mikinty/Omega3/images/IMG_20180331_031521.jpg

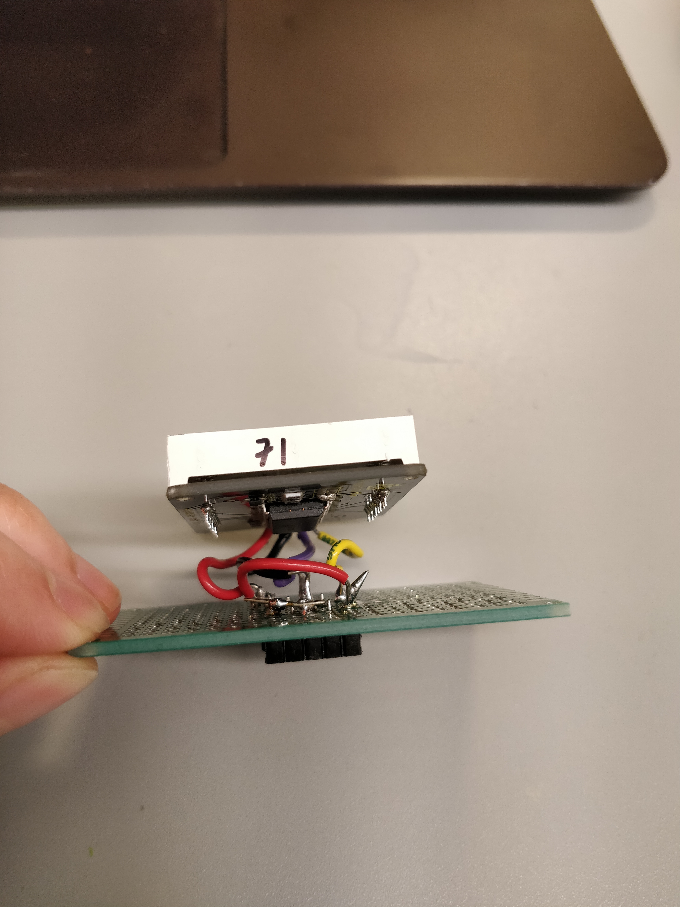
images/IMG_20180331_031521.jpg
