mikinty/Omega3/images/IMG_20180331_031531.jpg

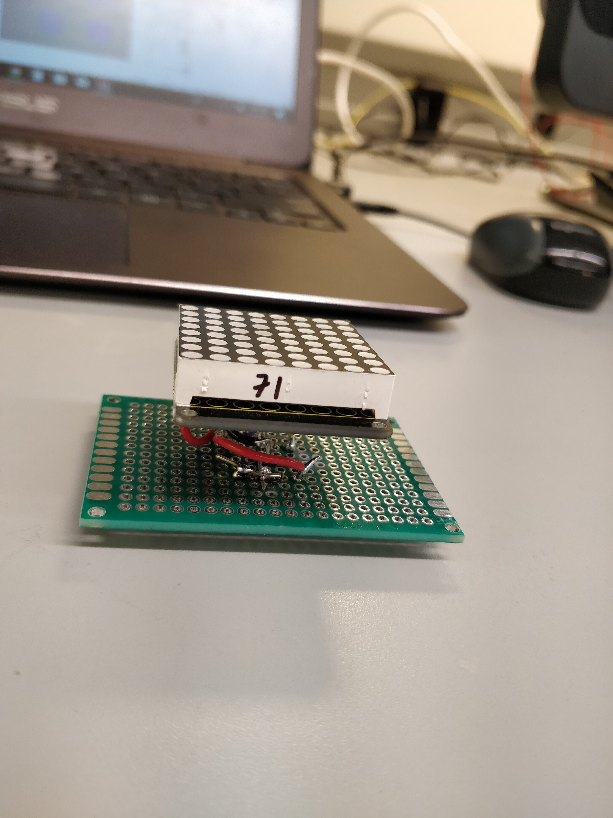
images/IMG_20180331_031531.jpg
