mikinty/Omega3/images/IMG_20180331_031629.jpg

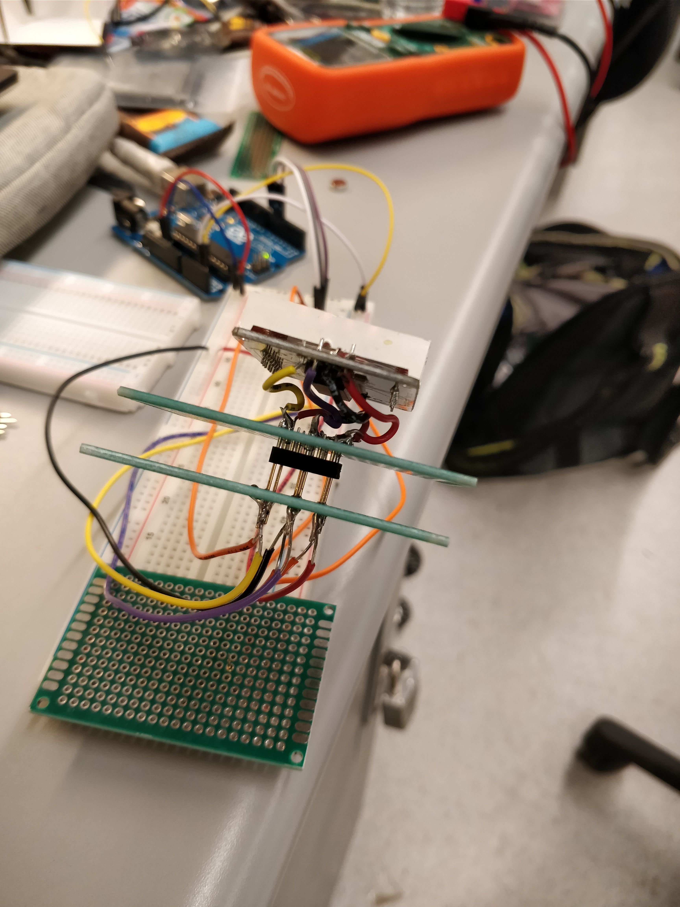
images/IMG_20180331_031629.jpg
