mikinty/Omega3/images/IMG_20180331_221203.jpg

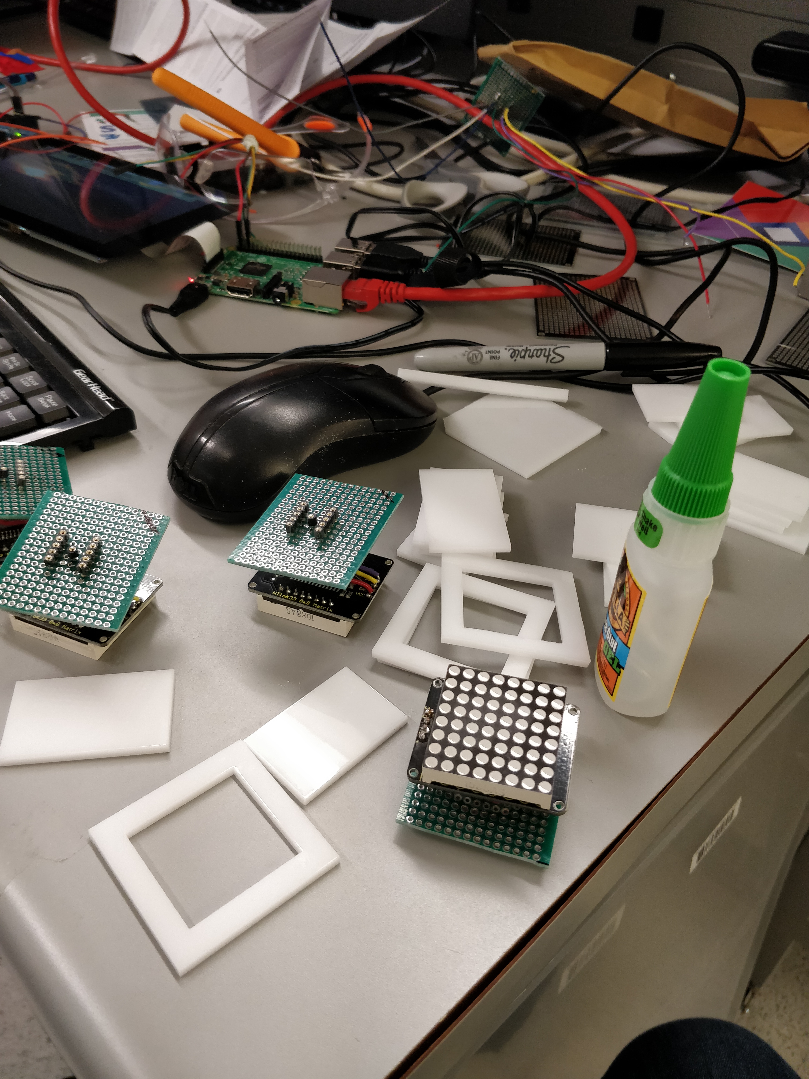
images/IMG_20180331_221203.jpg
