mikinty/Omega3/images/IMG_20180331_233230.jpg

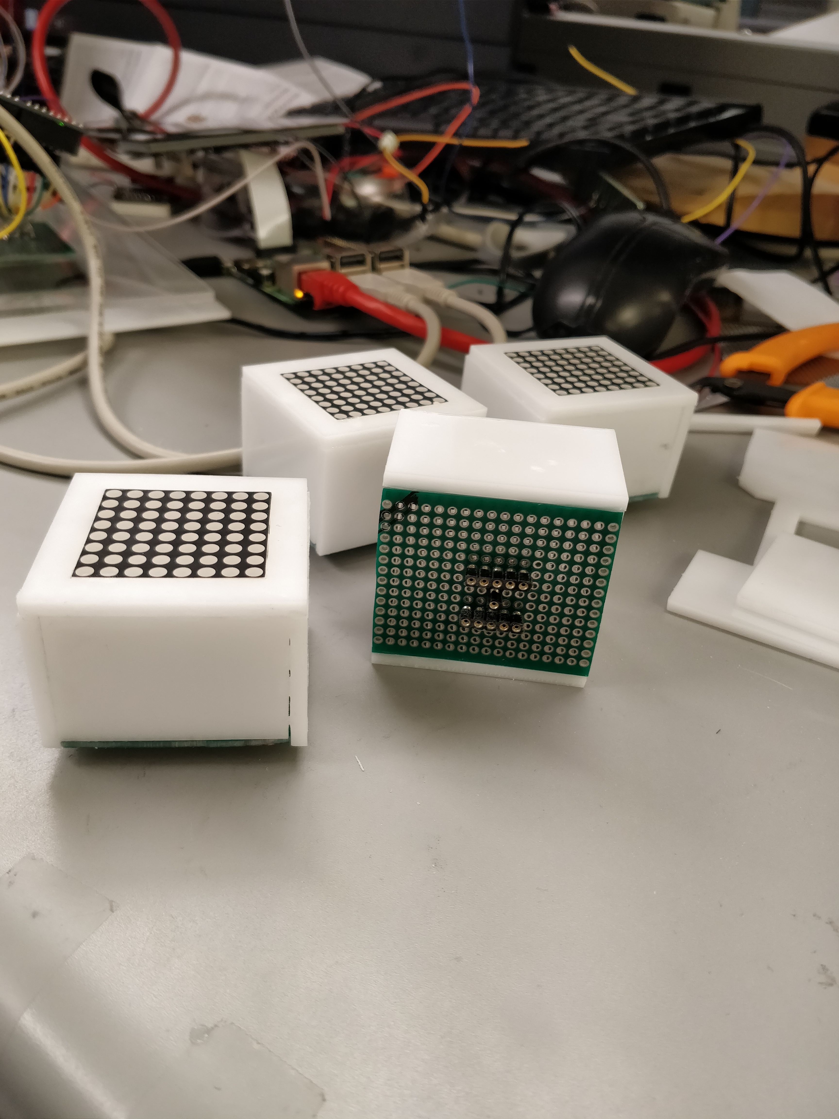
images/IMG_20180331_233230.jpg
