mikinty/Omega3/images/IMG_20180331_233232.jpg

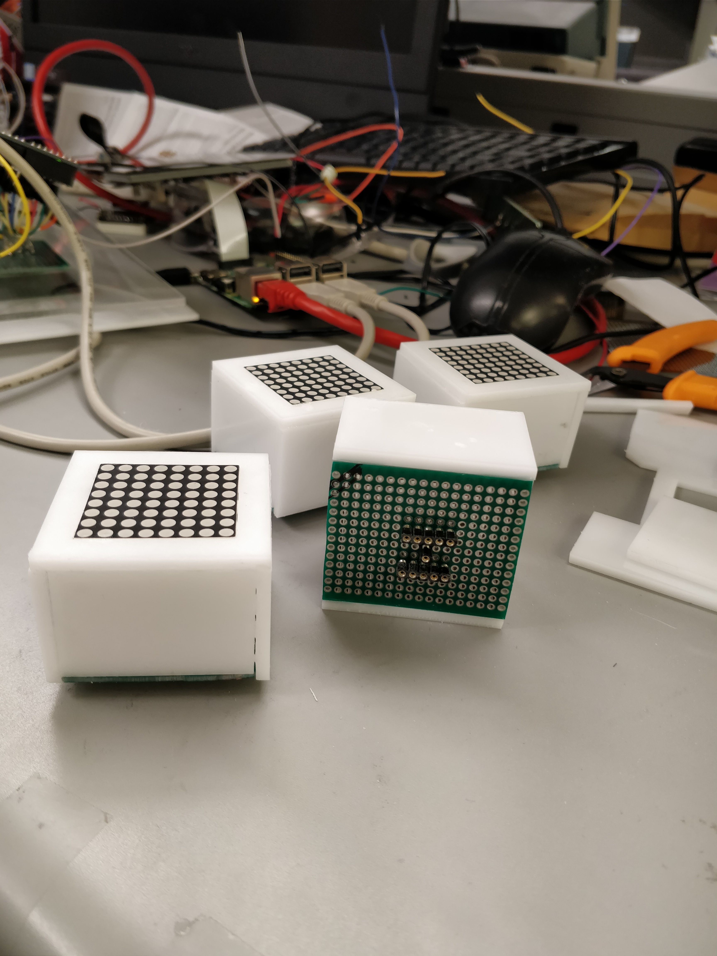
images/IMG_20180331_233232.jpg
