mikinty/Omega3/images/IMG_20180401_004014.jpg

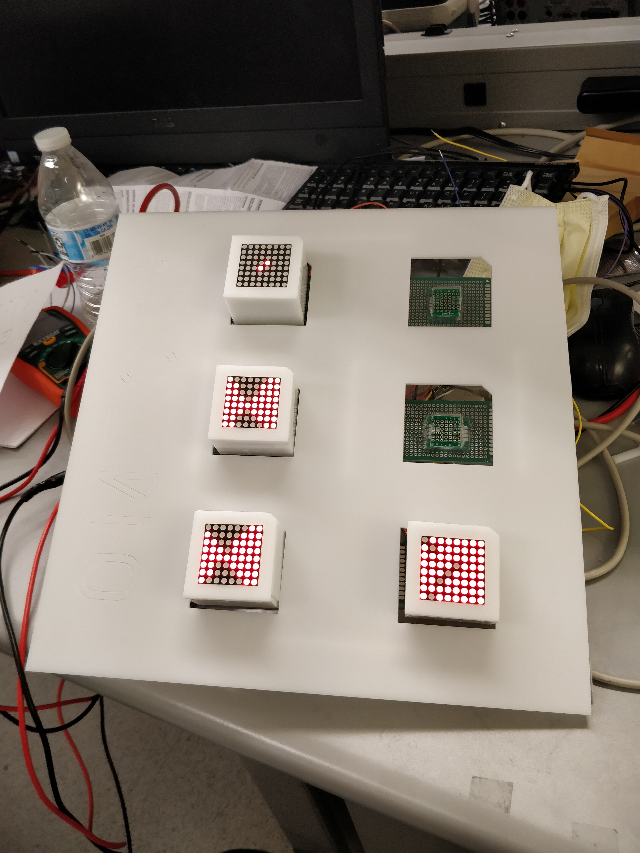
images/IMG_20180401_004014.jpg
