mikinty/Omega3/images/IMG_20180401_004016.jpg

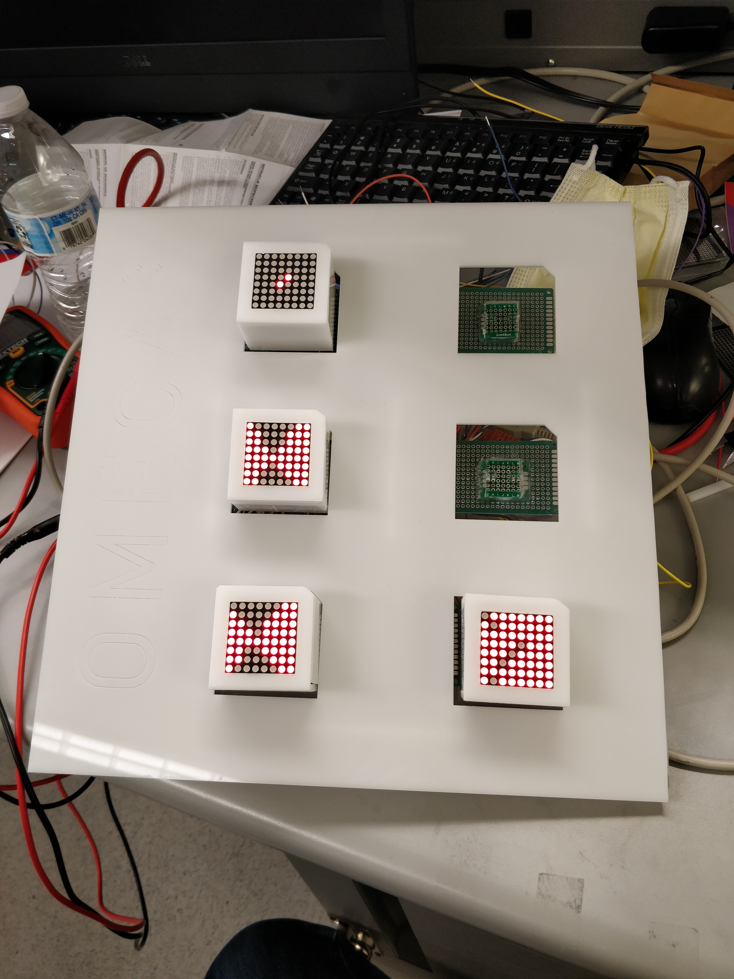
images/IMG_20180401_004016.jpg
