mikinty/Omega3/images/IMG_20180401_004311.jpg

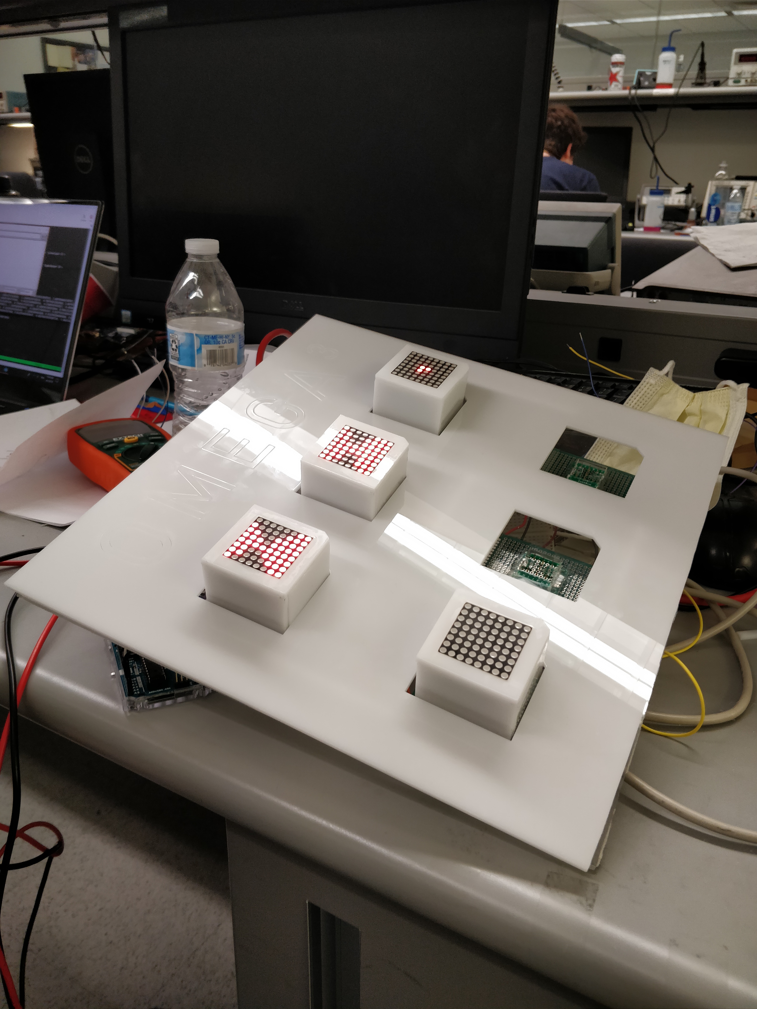
images/IMG_20180401_004311.jpg
