mikinty/Omega3/images/IMG_20180401_020950.jpg

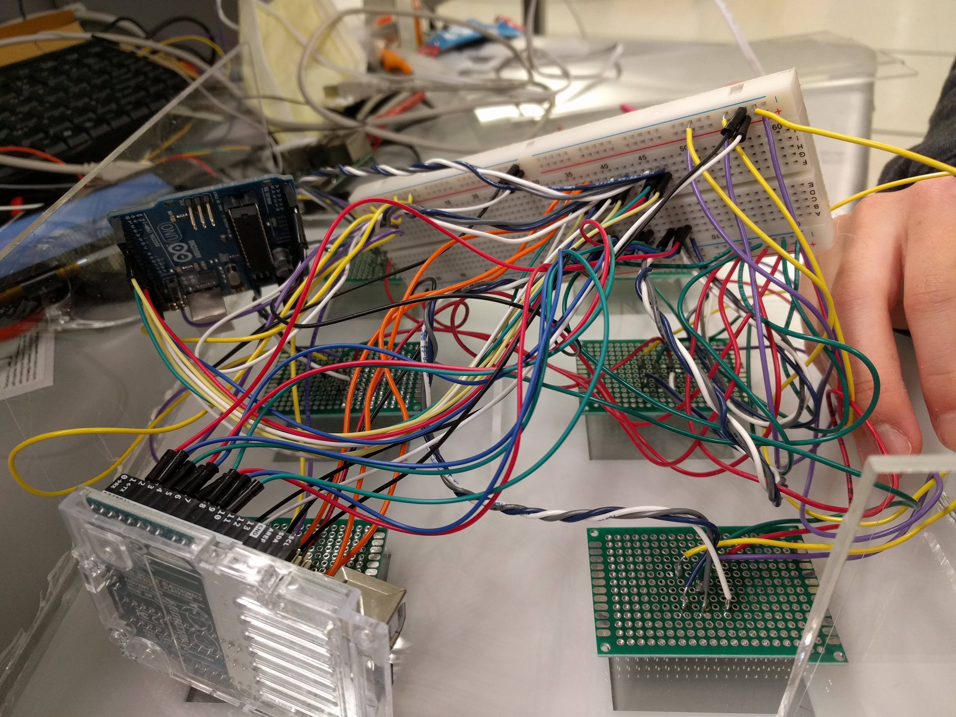
images/IMG_20180401_020950.jpg
