mikinty/Omega3/images/IMG_20180401_051516.jpg

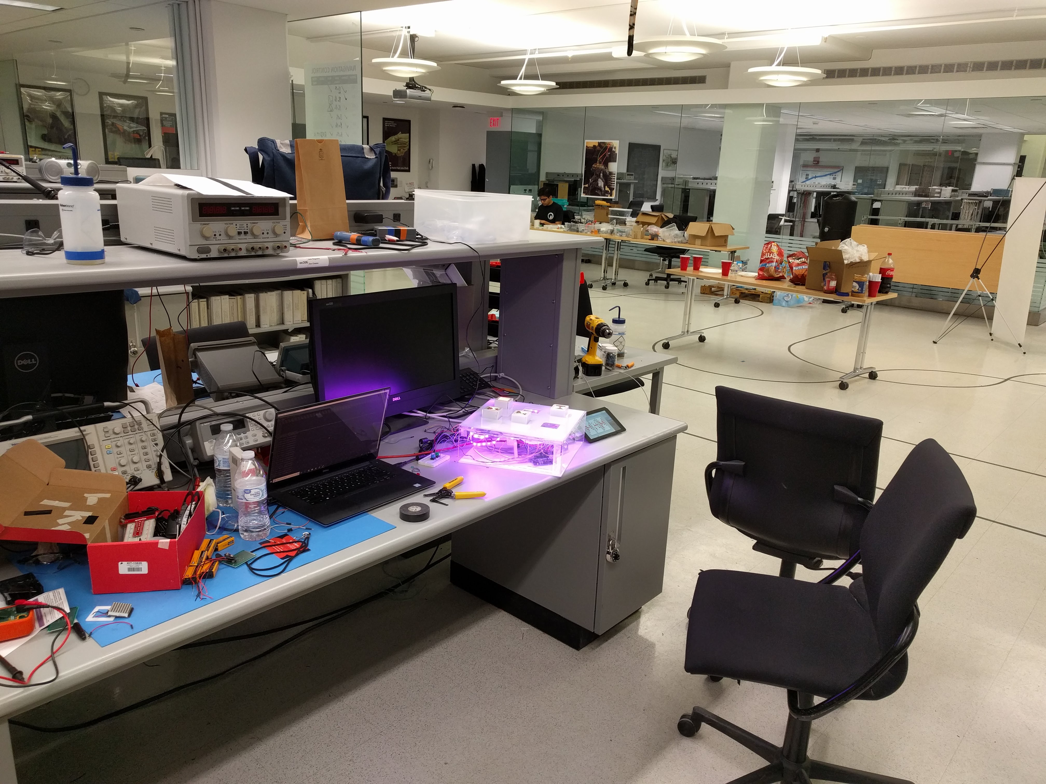
images/IMG_20180401_051516.jpg
