mikinty/Omega3/images/IMG_20180401_051522.jpg

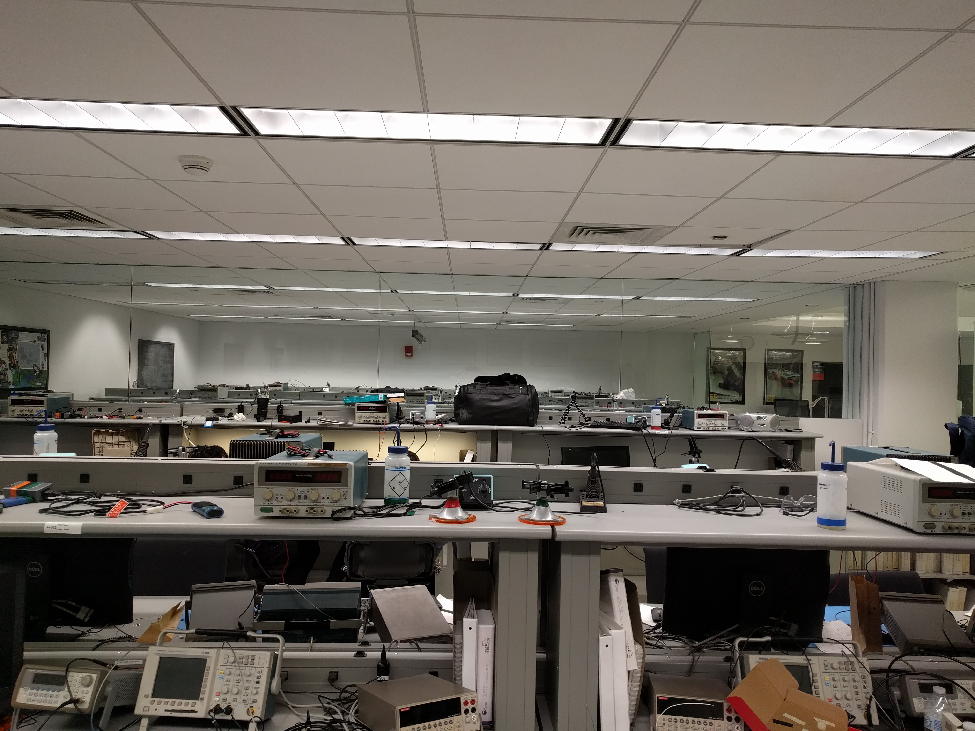
images/IMG_20180401_051522.jpg
