mikinty/Omega3/images/IMG_20180401_051529.jpg

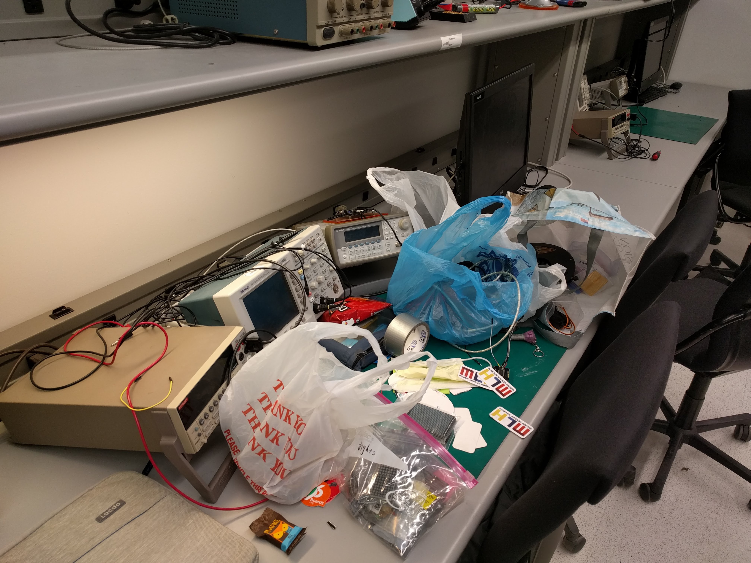
images/IMG_20180401_051529.jpg
