mikinty/Omega3/images/IMG_20180401_070534.jpg

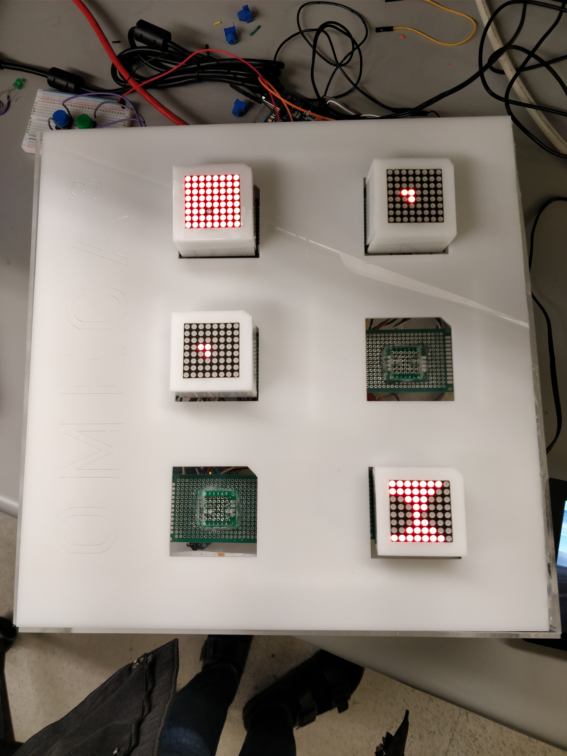
images/IMG_20180401_070534.jpg
