mikinty/Omega3/images/IMG_20180401_070551.jpg

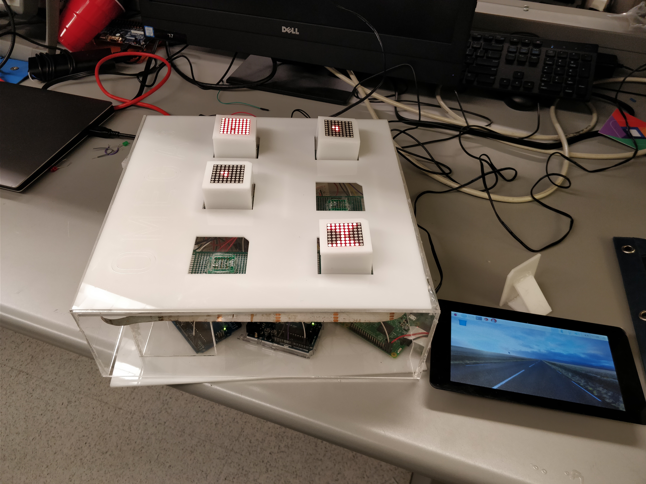
images/IMG_20180401_070551.jpg
