mikinty/Omega3/images/IMG_20180401_070601.jpg

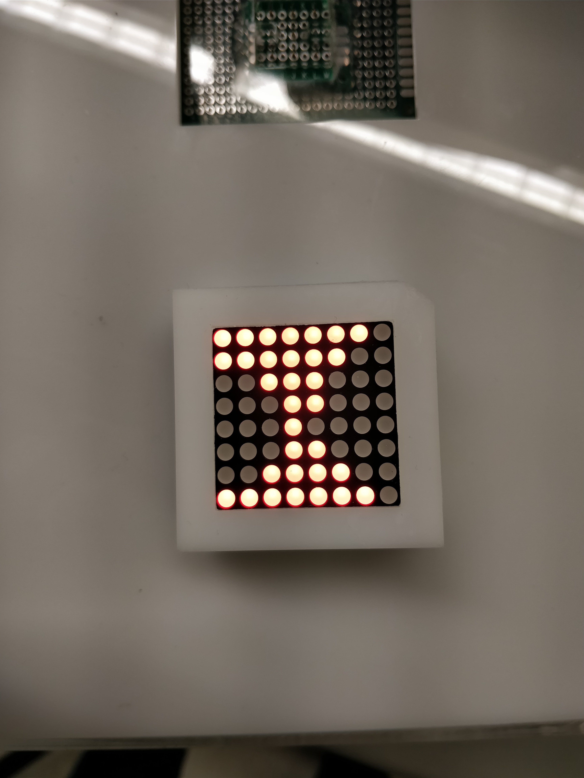
images/IMG_20180401_070601.jpg
