mikinty/Omega3/images/IMG_20180401_070608.jpg

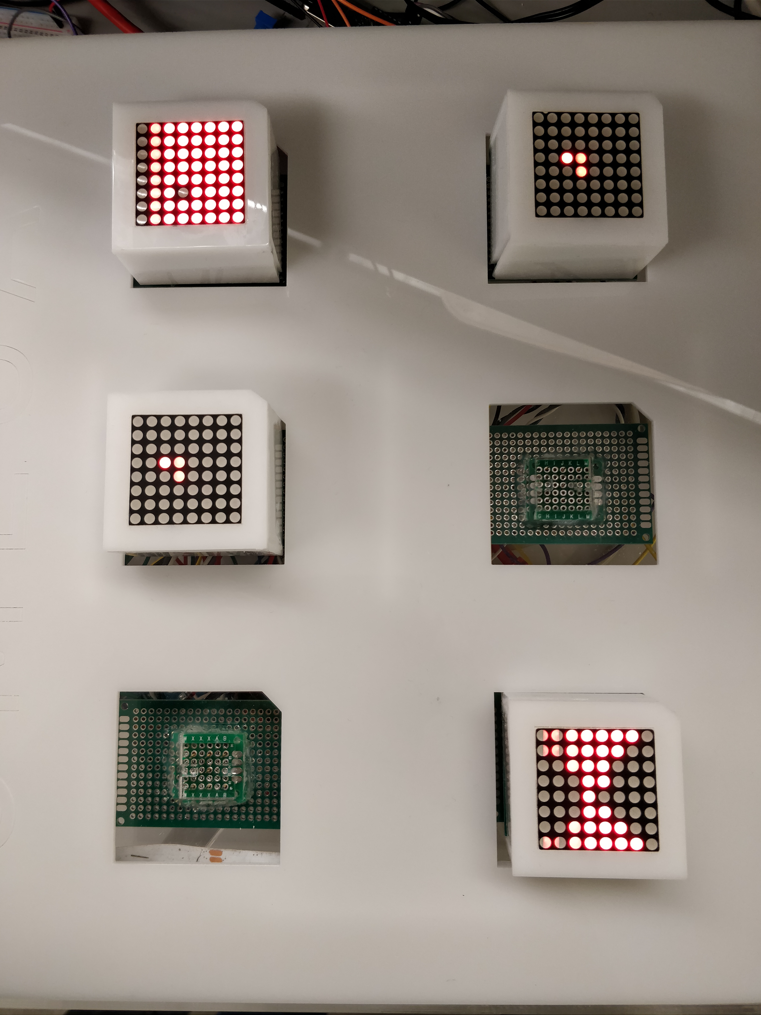
images/IMG_20180401_070608.jpg
