mikinty/Omega3/images/IMG_20180401_071721.jpg

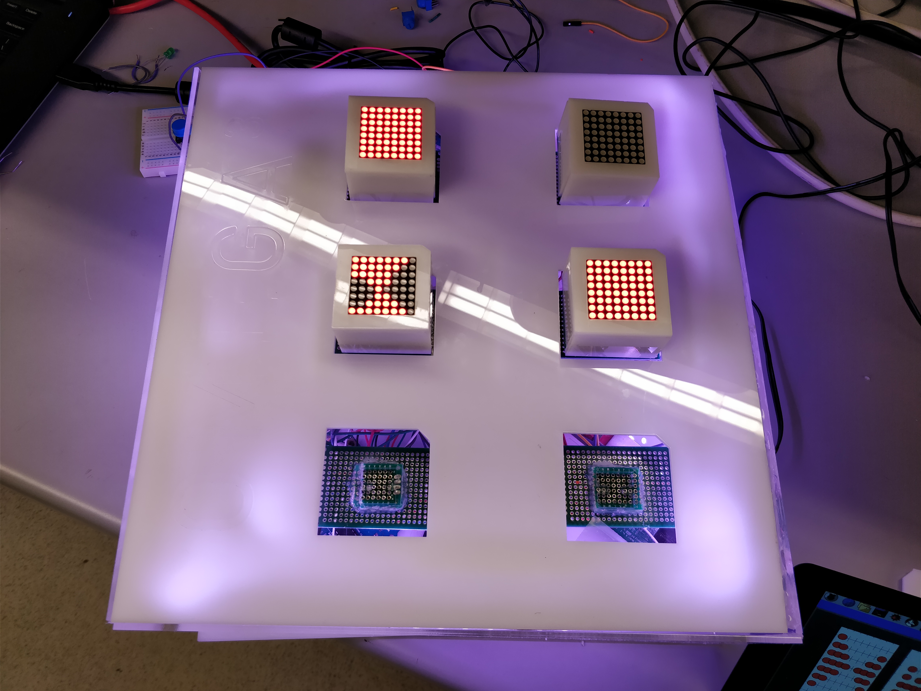
images/IMG_20180401_071721.jpg
