mikinty/Omega3/images/IMG_20180401_071728.jpg

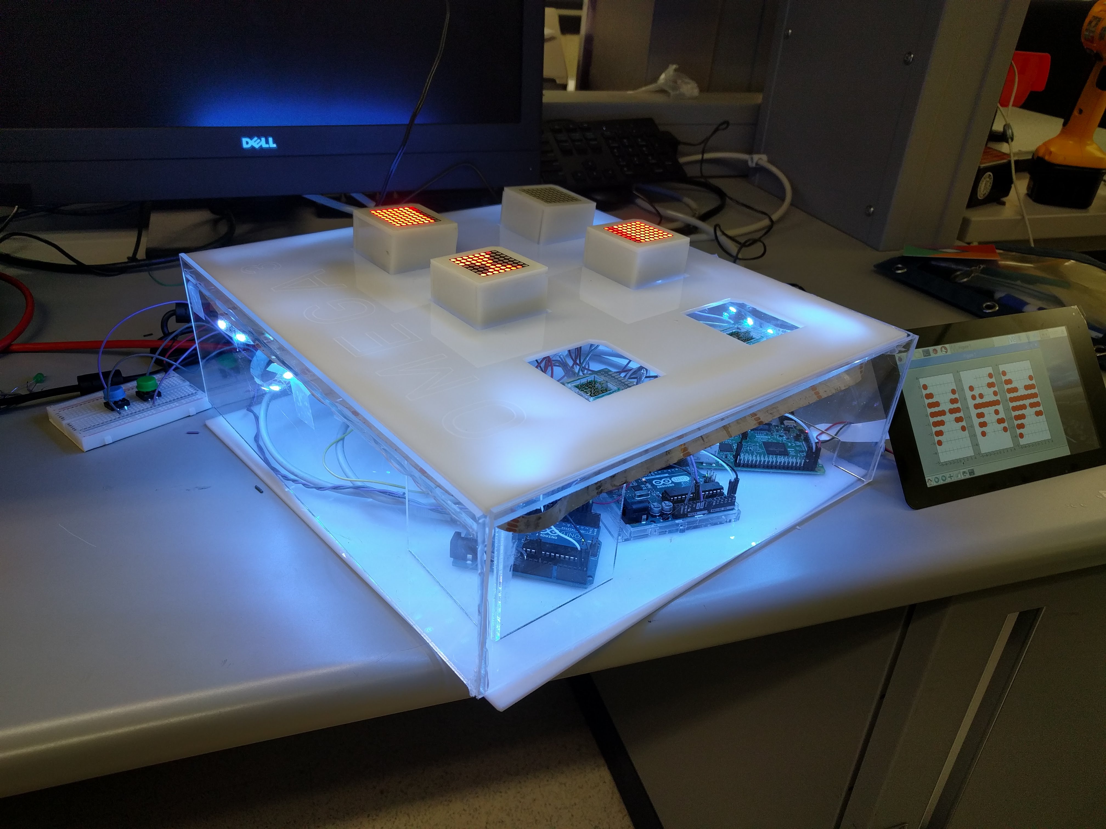
images/IMG_20180401_071728.jpg
