mikinty/Omega3/images/IMG_20180401_071740.jpg

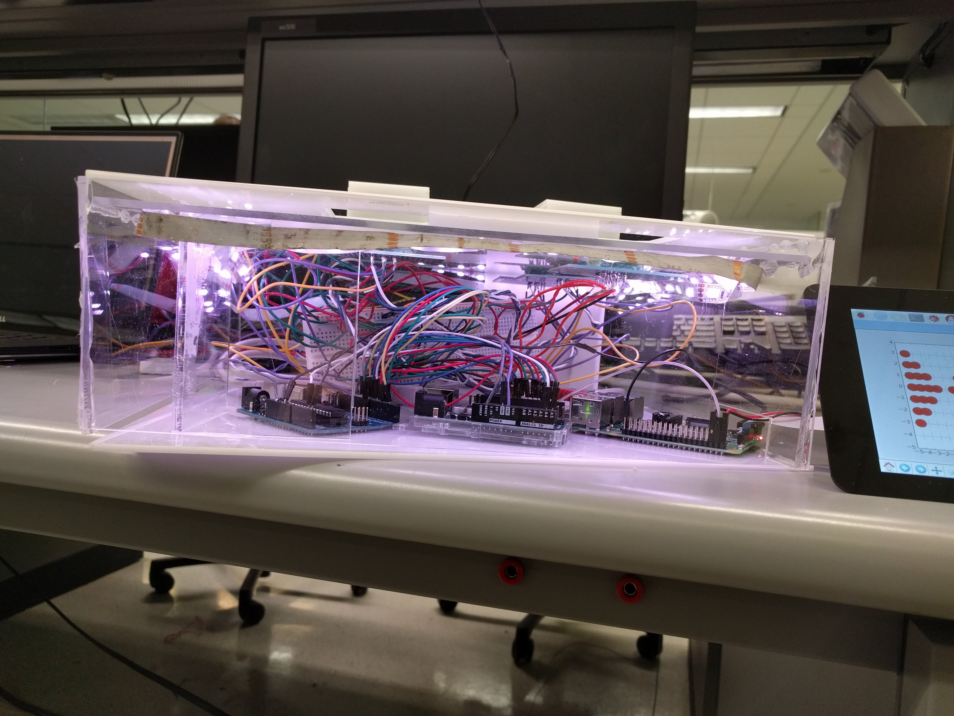
images/IMG_20180401_071740.jpg
