mikinty/Omega3/images/IMG_20180401_071742.jpg

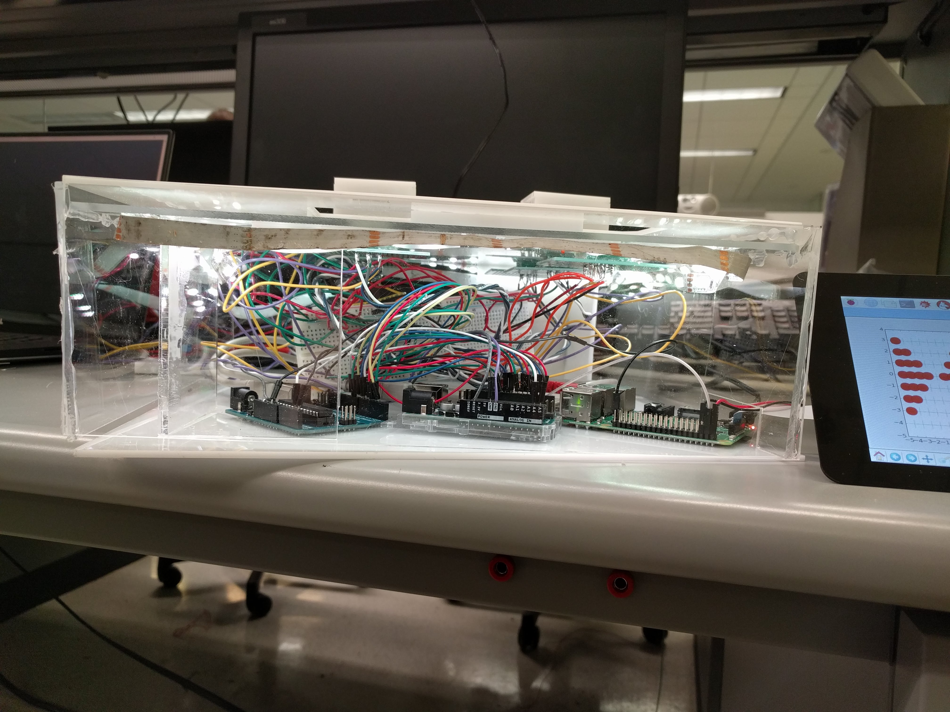
images/IMG_20180401_071742.jpg
