mikinty/Omega3/images/IMG_20180401_071747.jpg

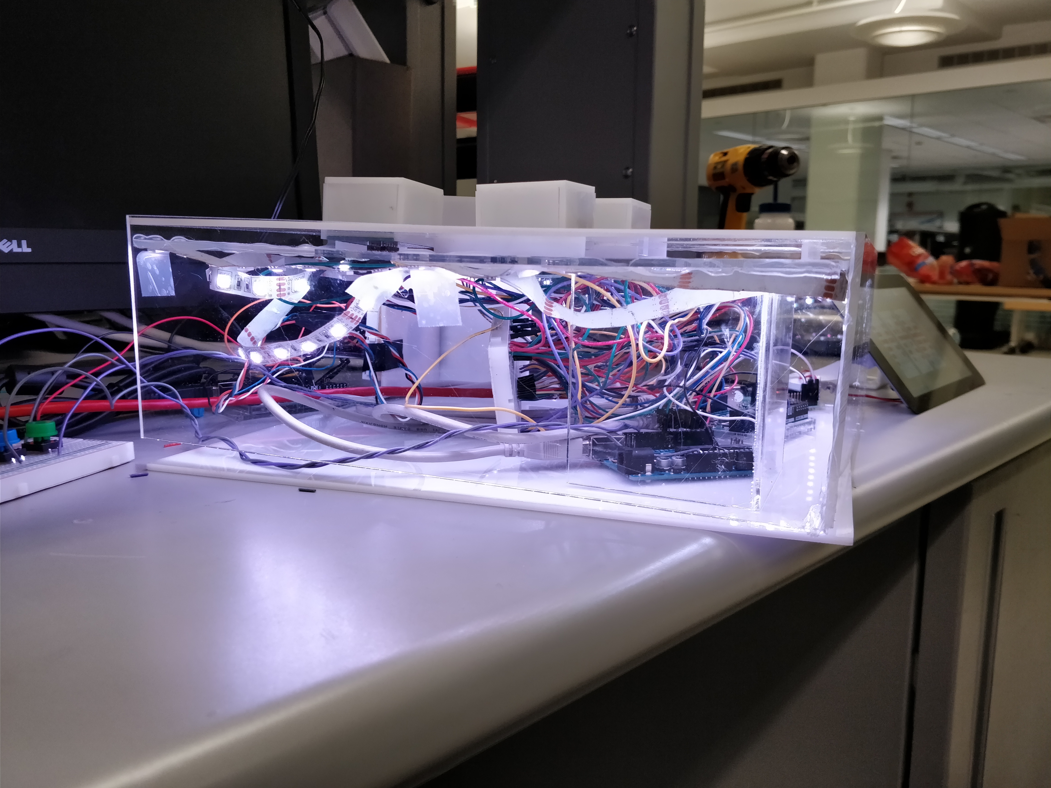
images/IMG_20180401_071747.jpg
