mikinty/Omega3/images/IMG_20180401_071758.jpg

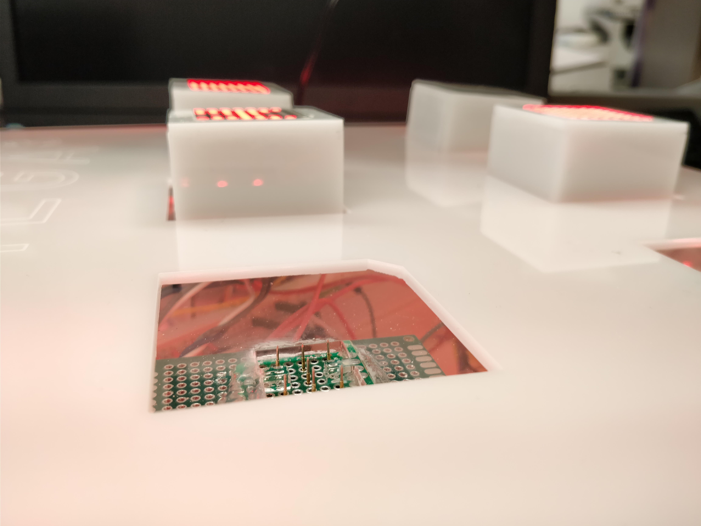
images/IMG_20180401_071758.jpg
