mikinty/Omega3/images/IMG_20180401_071807.jpg

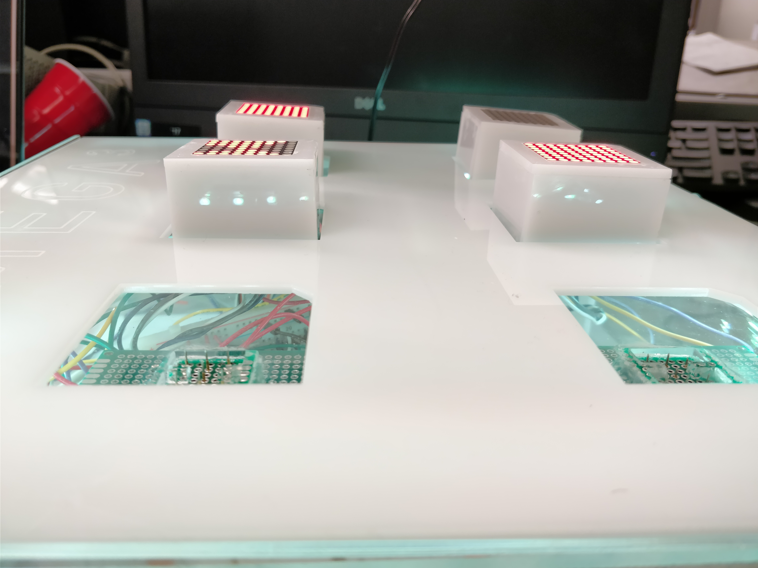
images/IMG_20180401_071807.jpg
