mikinty/Omega3/images/omega32.jpg

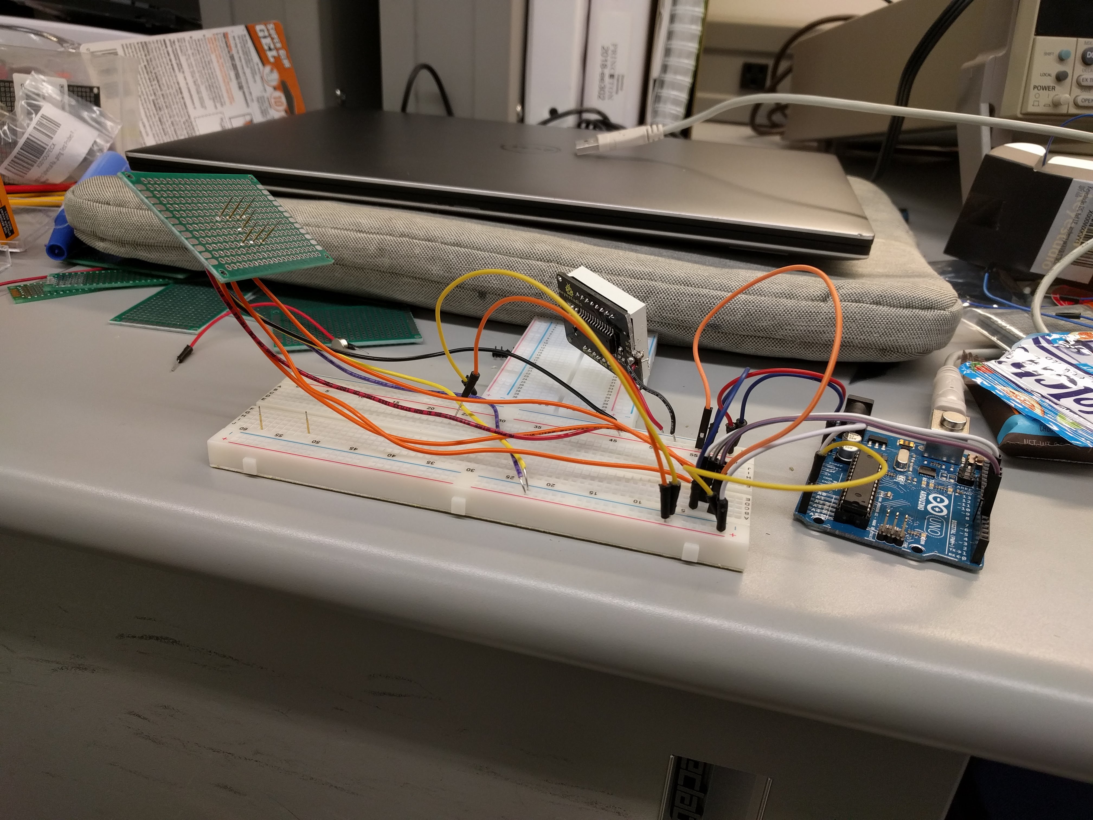
images/omega32.jpg
