mikinty/Omega3/paper/images/base_exploded.JPG

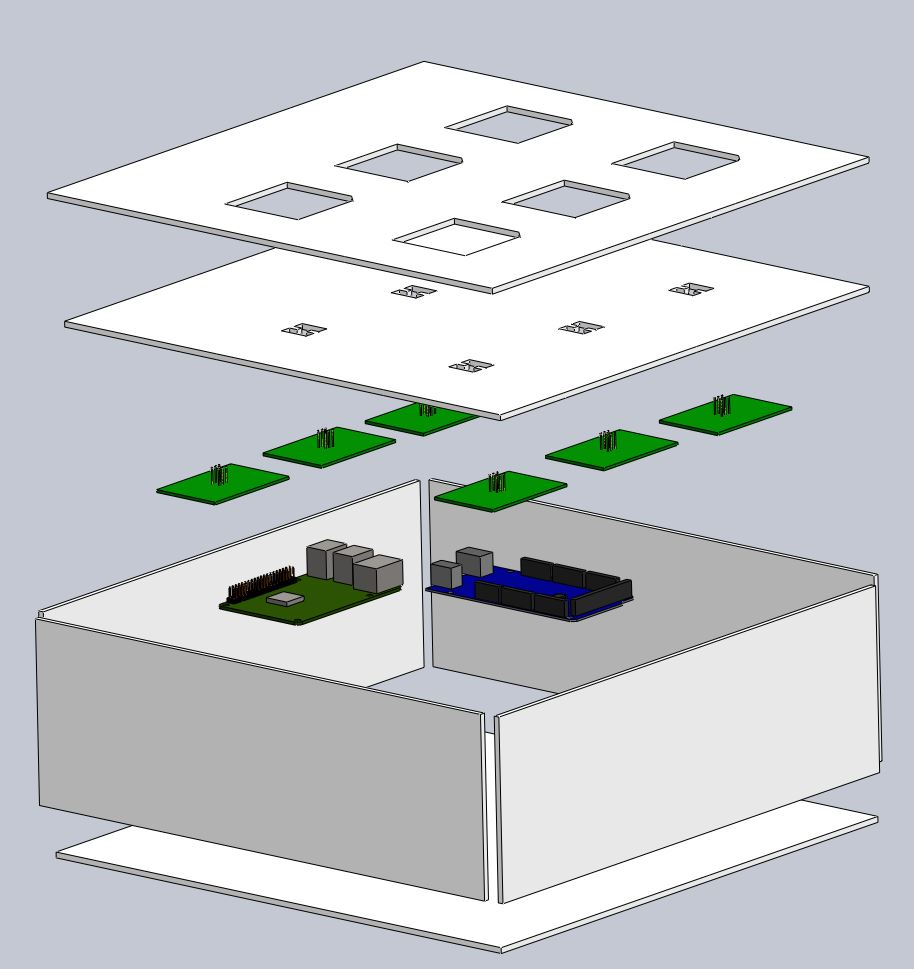
paper/images/base_exploded.JPG
