mikinty/Omega3/paper/images/pins.png

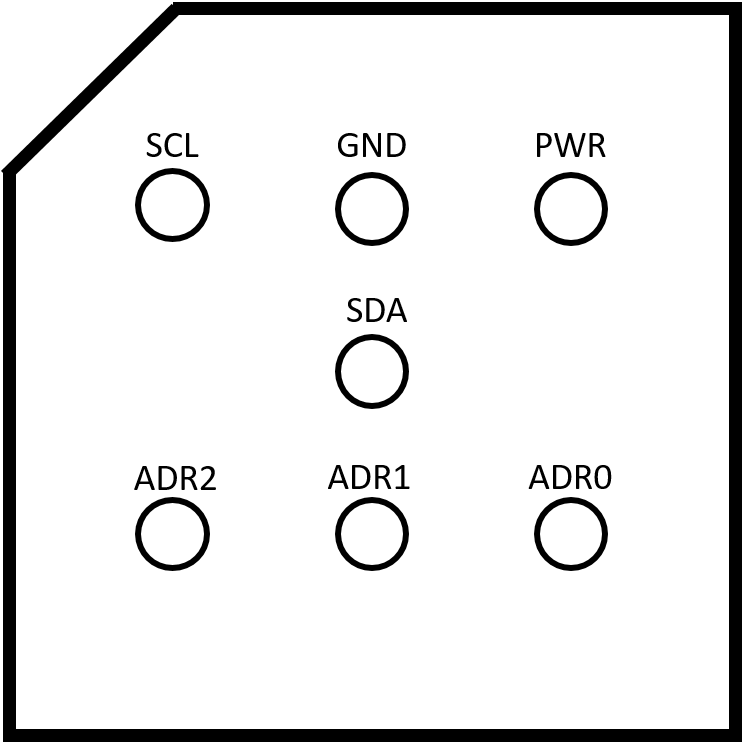
paper/images/pins.png
