mikinty/Omega3/CAD files/middlesupports.SLDPRT

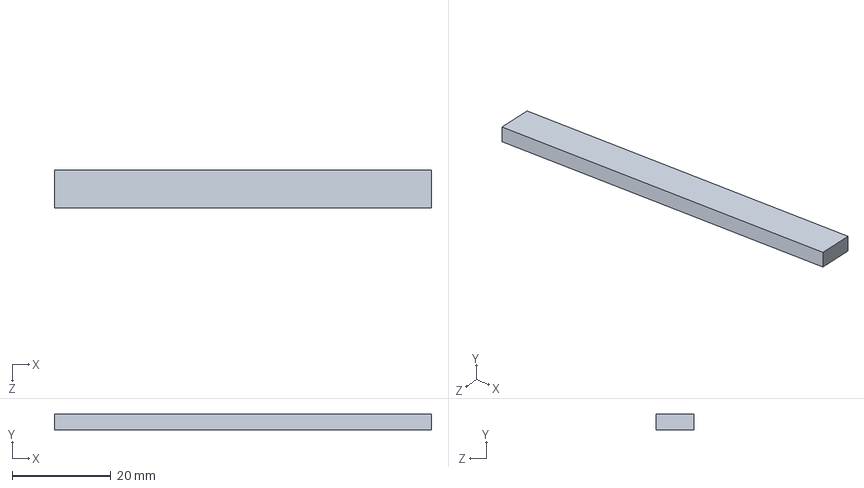
[picture p52: CAD file, 2018-04-03]
CAD files/middlesupports.SLDPRT
76.2 x 3.17 x 7.62 mm
