mikinty/Omega3/CAD files/topboard.SLDPRT

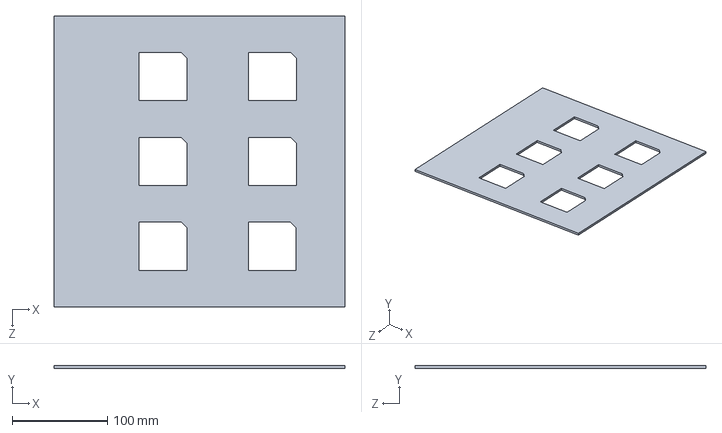
[picture p53: CAD file, 2018-04-03]
CAD files/topboard.SLDPRT
304.8 x 3.17 x 304.8 mm
