mikinty/Omega3/paper/images/socket_wiring_v4.png

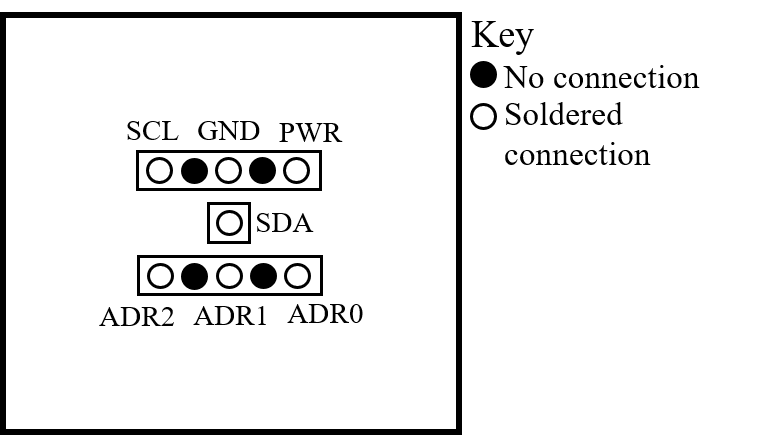
paper/images/socket_wiring_v4.png
