mikinty/Omega3/paper/images/wiring.png

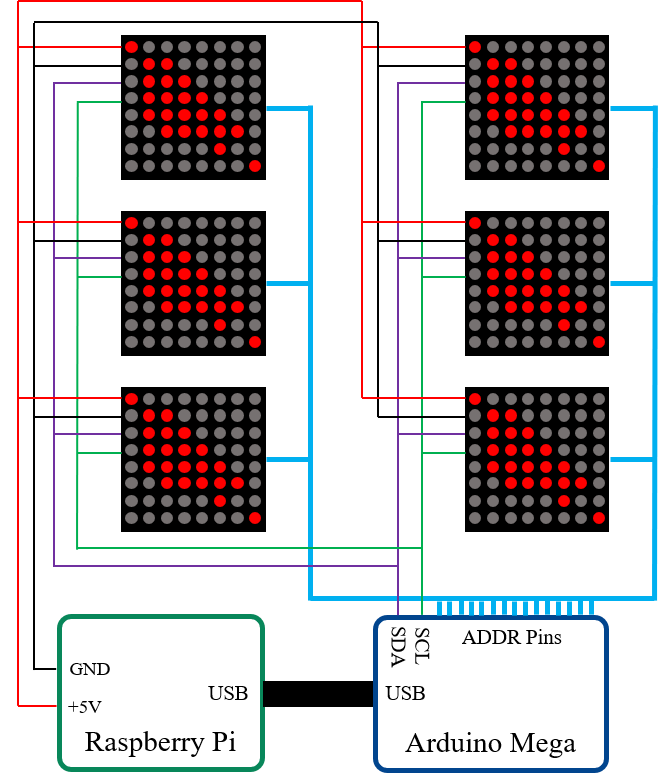
paper/images/wiring.png
